Kevi33/NAS/exports/individual/STEP/mid_frame.step

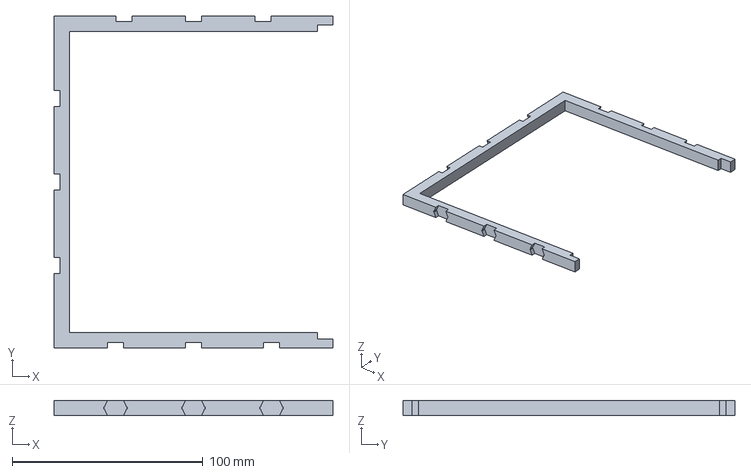
[picture p15: CAD file, 2026-08-13]
exports/individual/STEP/mid_frame.step
146.0 x 174.0 x 8.00 mm
