Kevi33/NAS/exports/individual/STEP/top_rear.step

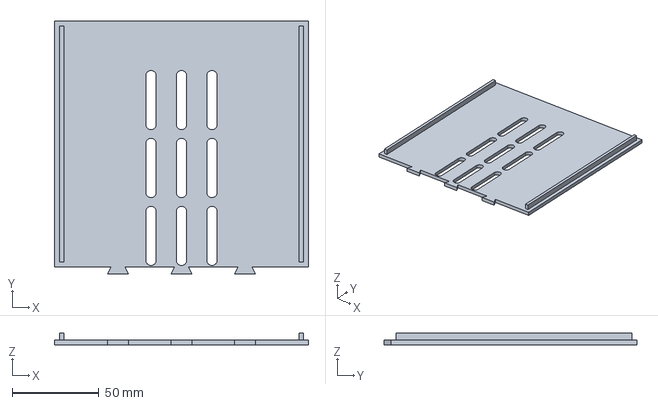
[picture p16: CAD file, 2026-08-13]
exports/individual/STEP/top_rear.step
146.0 x 145.6 x 6.80 mm
