Kevi33/NAS/exports/individual/STEP/left_side_front.step

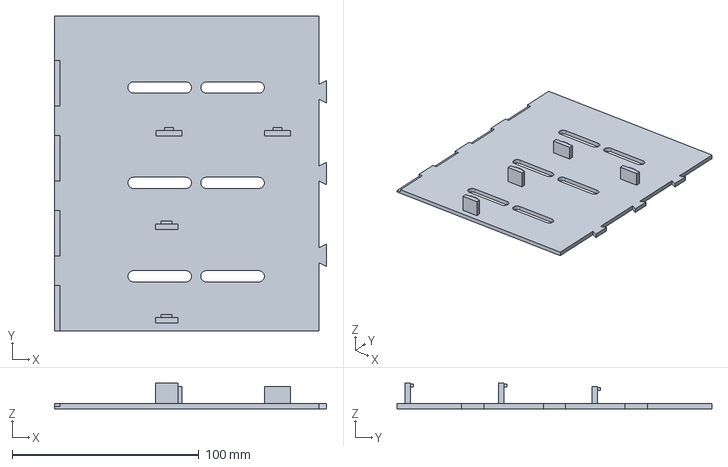
[picture p17: CAD file, 2026-08-13]
exports/individual/STEP/left_side_front.step
145.6 x 168.4 x 13.8 mm
