Kevi33/NAS/exports/individual/STEP/right_side_rear.step

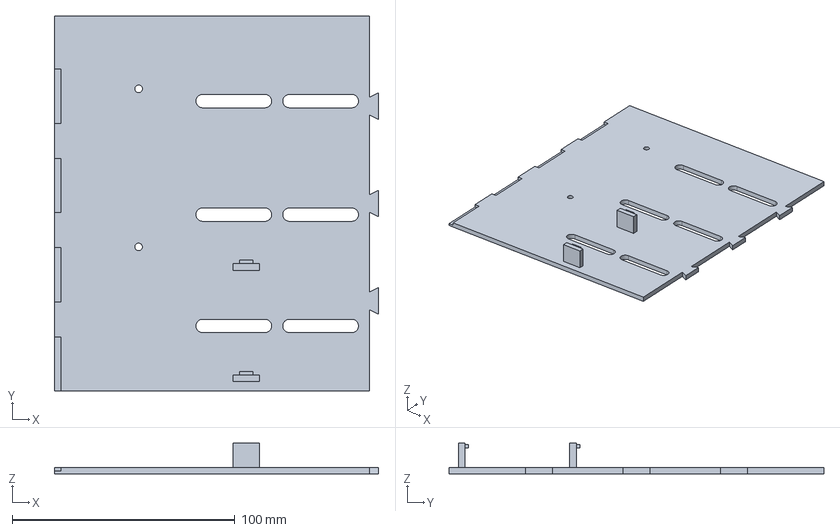
[picture p18: CAD file, 2026-08-13]
exports/individual/STEP/right_side_rear.step
145.6 x 168.4 x 13.8 mm
