Kevi33/NAS/exports/individual/STEP/hdd_tray_rear.step

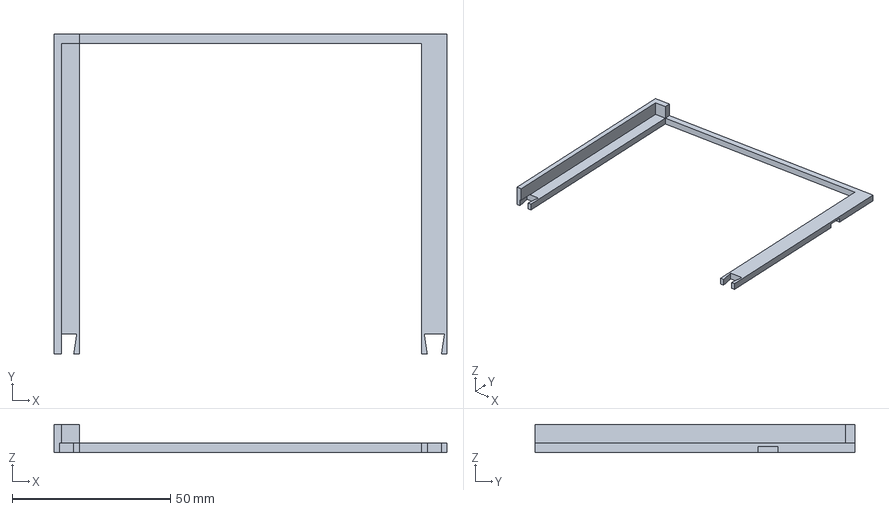
[picture p19: CAD file, 2026-08-13]
exports/individual/STEP/hdd_tray_rear.step
124.3 x 101.2 x 9.00 mm
