Kevi33/NAS/exports/individual/STEP/rear_panel.step

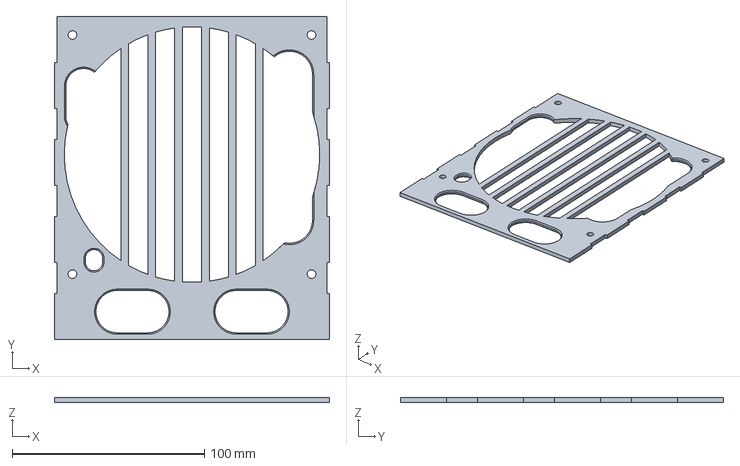
[picture p20: CAD file, 2026-08-13]
exports/individual/STEP/rear_panel.step
143.2 x 168.4 x 2.80 mm
