Kevi33/NAS/exports/individual/STEP/cable_clip.step

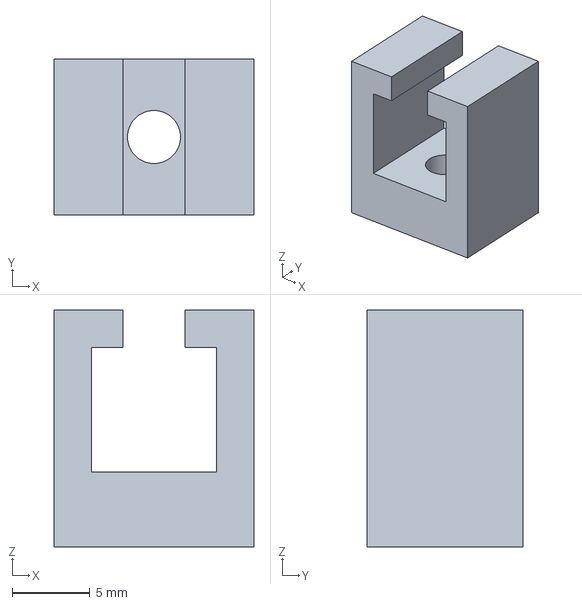
[picture p21: CAD file, 2026-08-13]
exports/individual/STEP/cable_clip.step
12.8 x 10.0 x 15.2 mm
