Kevi33/NAS/exports/individual/STEP/usb_hub_mount.step

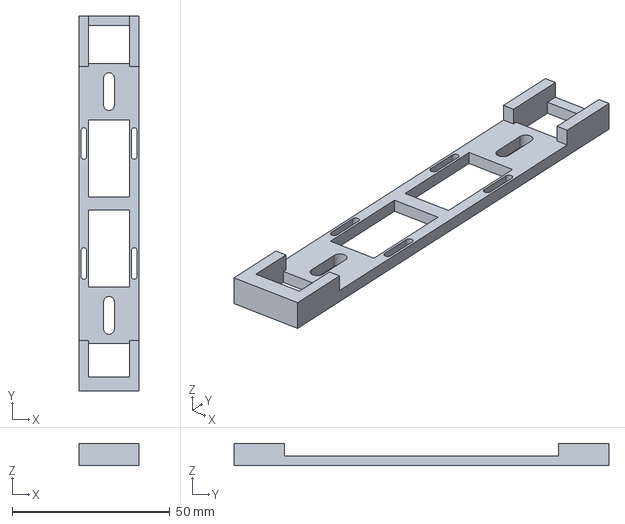
[picture p22: CAD file, 2026-08-13]
exports/individual/STEP/usb_hub_mount.step
19.0 x 119.0 x 7.00 mm
