Kevi33/NAS/exports/individual/STEP/rear_fan_guard.step

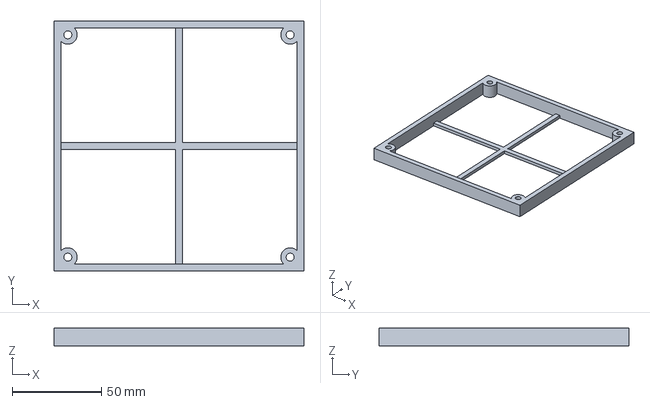
[picture p23: CAD file, 2026-08-13]
exports/individual/STEP/rear_fan_guard.step
140.0 x 140.0 x 10.0 mm
