Kevi33/NAS/exports/individual/STEP/foot.step

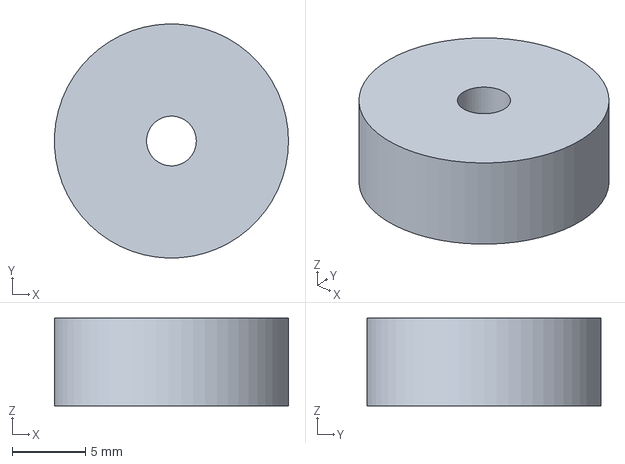
[picture p24: CAD file, 2026-08-13]
exports/individual/STEP/foot.step
16.0 x 16.0 x 6.00 mm
